MakeItHackin/DEFCON29Badge/pcb.jpg

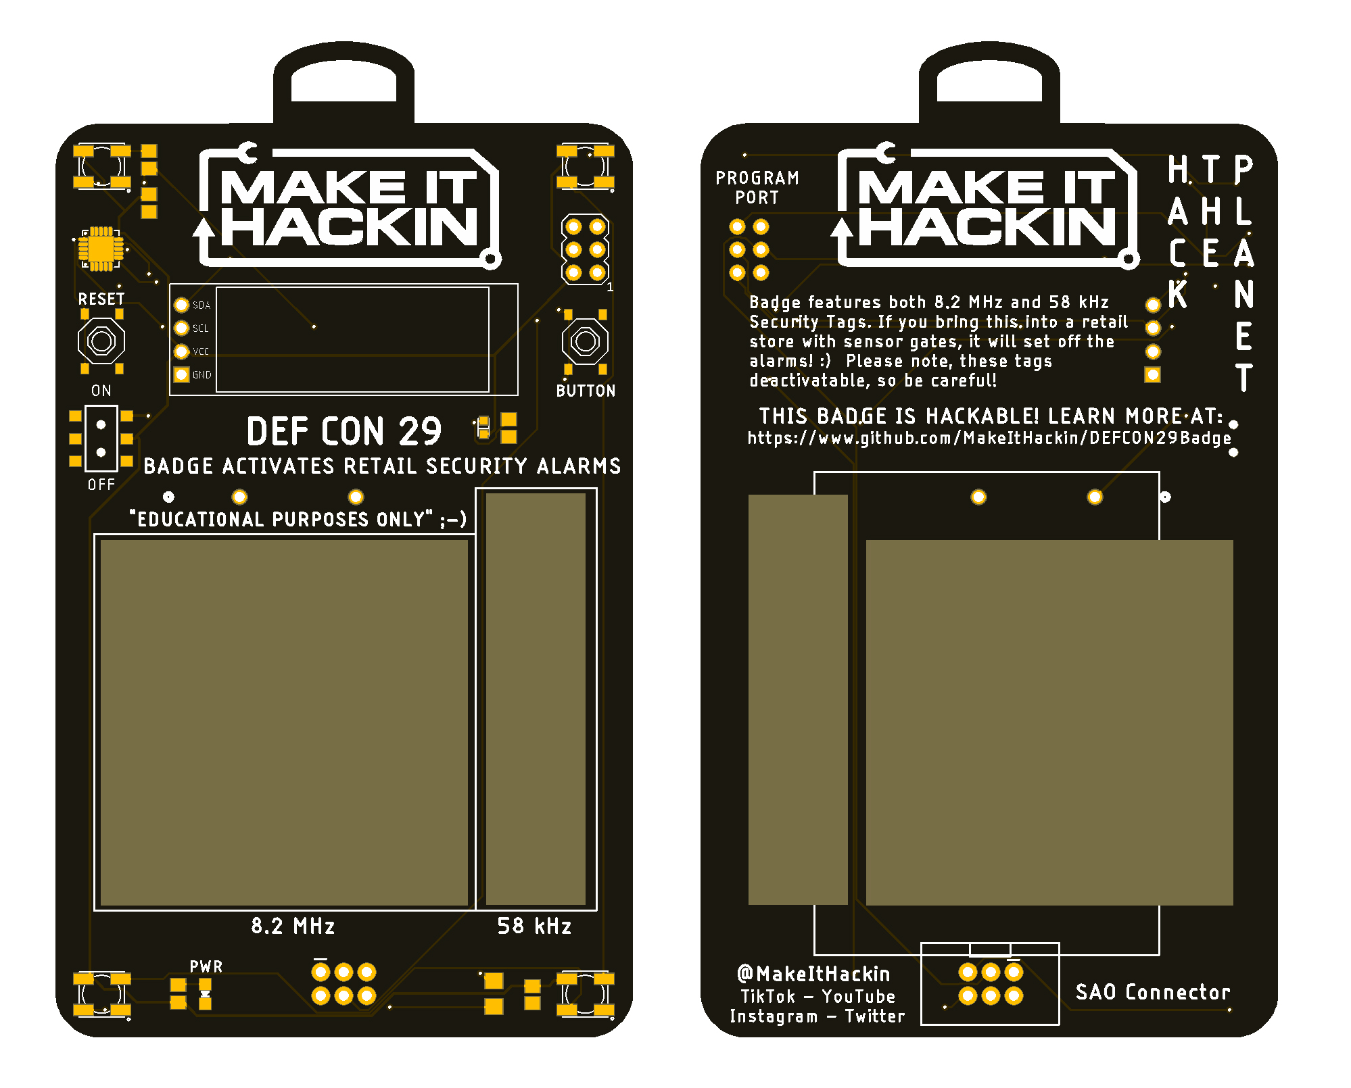
pcb.jpg
