MakeItHackin/DEFCON29Badge/Pictures/Kit/IMG_9323.jpeg

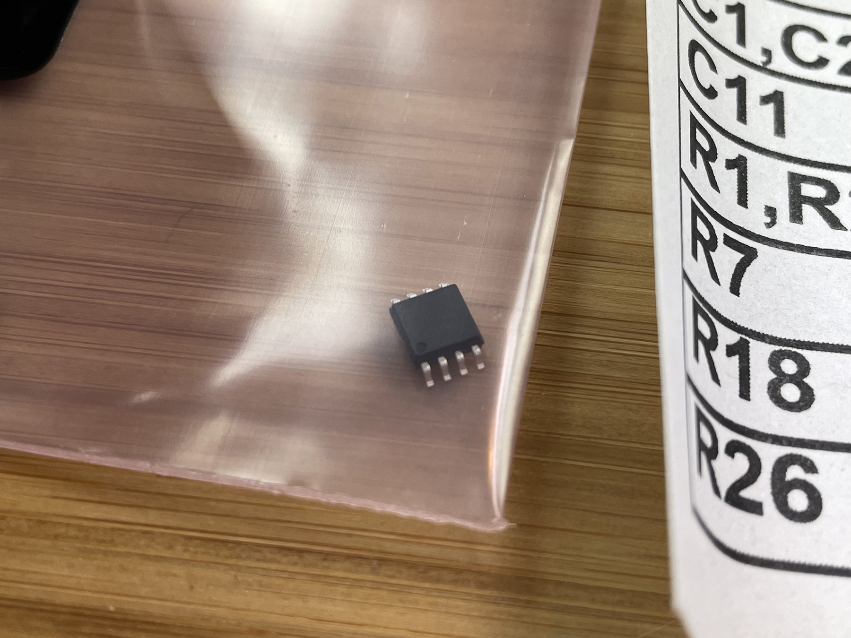
Pictures/Kit/IMG_9323.jpeg
