MakeItHackin/DEFCON29Badge/Pictures/Kit/IMG_9324.jpeg

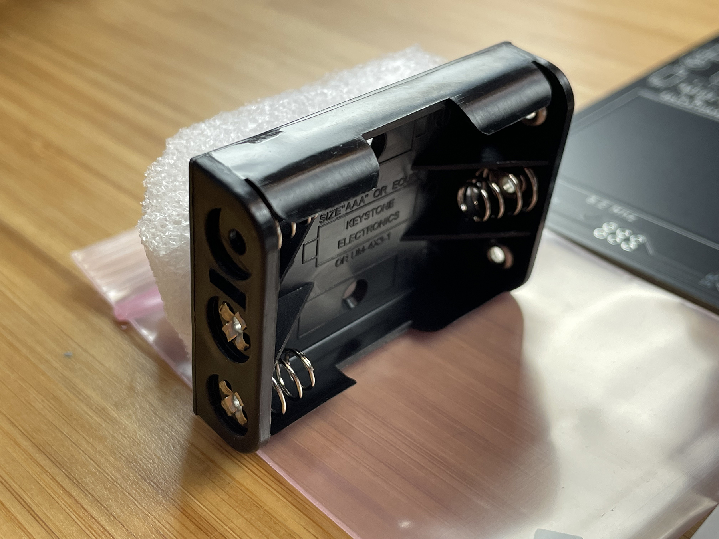
Pictures/Kit/IMG_9324.jpeg
