MakeItHackin/DEFCON29Badge/Pictures/Kit/IMG_9325.jpeg

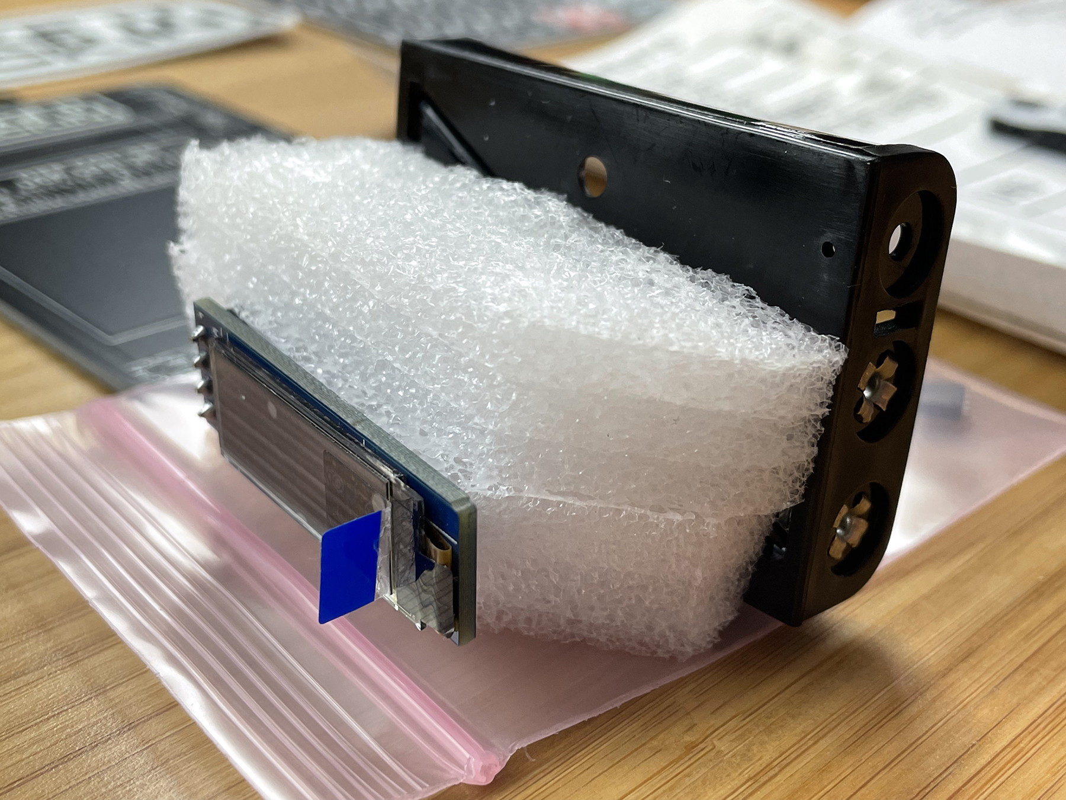
Pictures/Kit/IMG_9325.jpeg
