MakeItHackin/DEFCON29Badge/Pictures/Kit/IMG_9326.jpeg

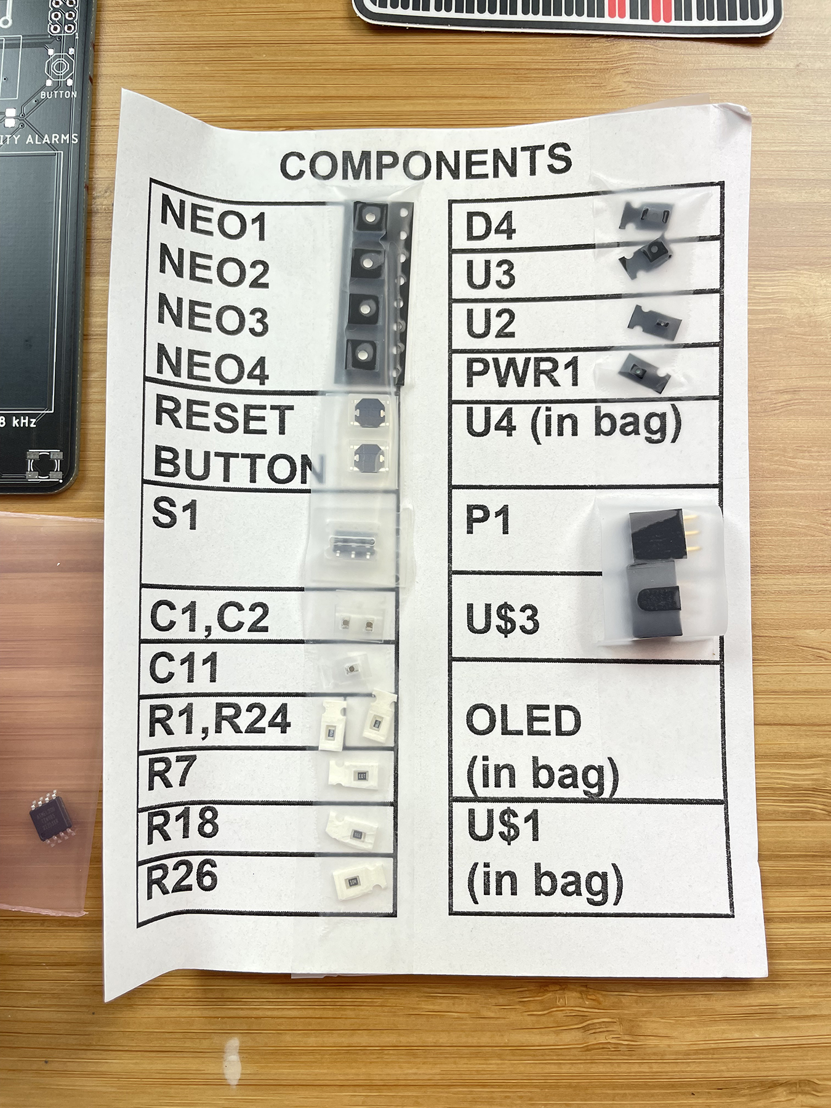
Pictures/Kit/IMG_9326.jpeg
