MakeItHackin/DEFCON29Badge/Pictures/Kit/IMG_9327.jpeg

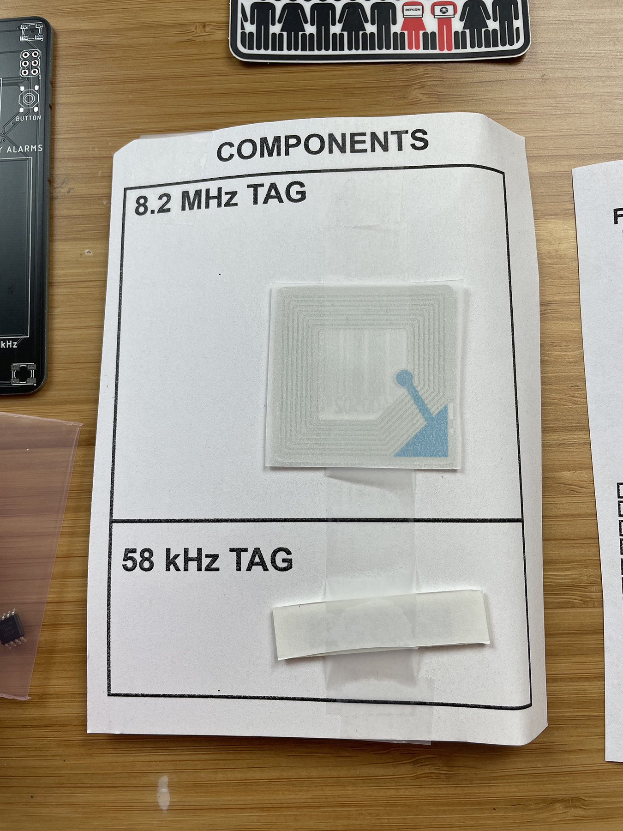
Pictures/Kit/IMG_9327.jpeg
