MakeItHackin/DEFCON29Badge/Pictures/Kit/IMG_9328.jpeg

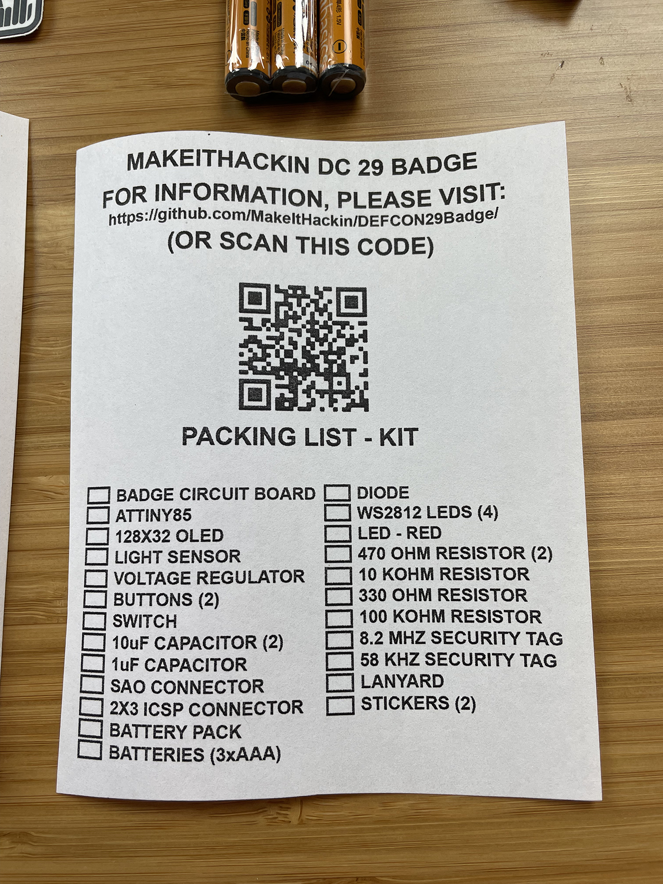
Pictures/Kit/IMG_9328.jpeg
