MakeItHackin/DEFCON29Badge/Pictures/Kit/IMG_9329.jpeg

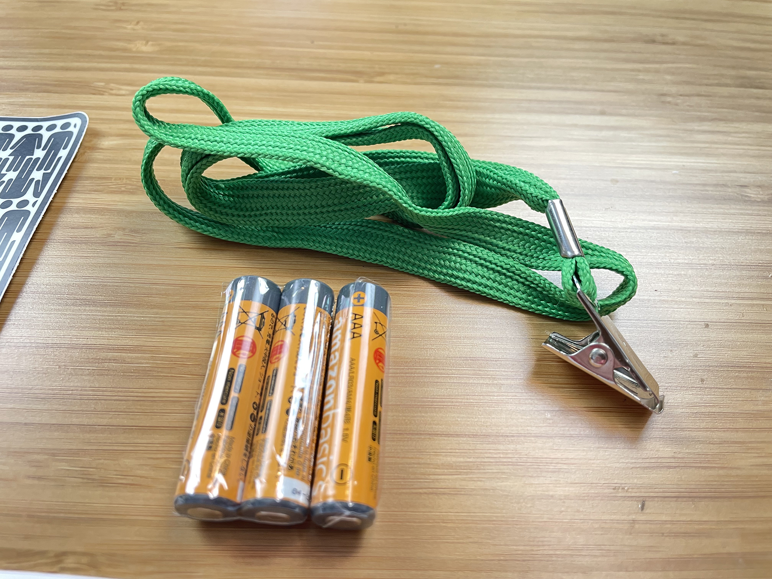
Pictures/Kit/IMG_9329.jpeg
