MakeItHackin/DEFCON29Badge/Pictures/Kit/kit pic.jpg

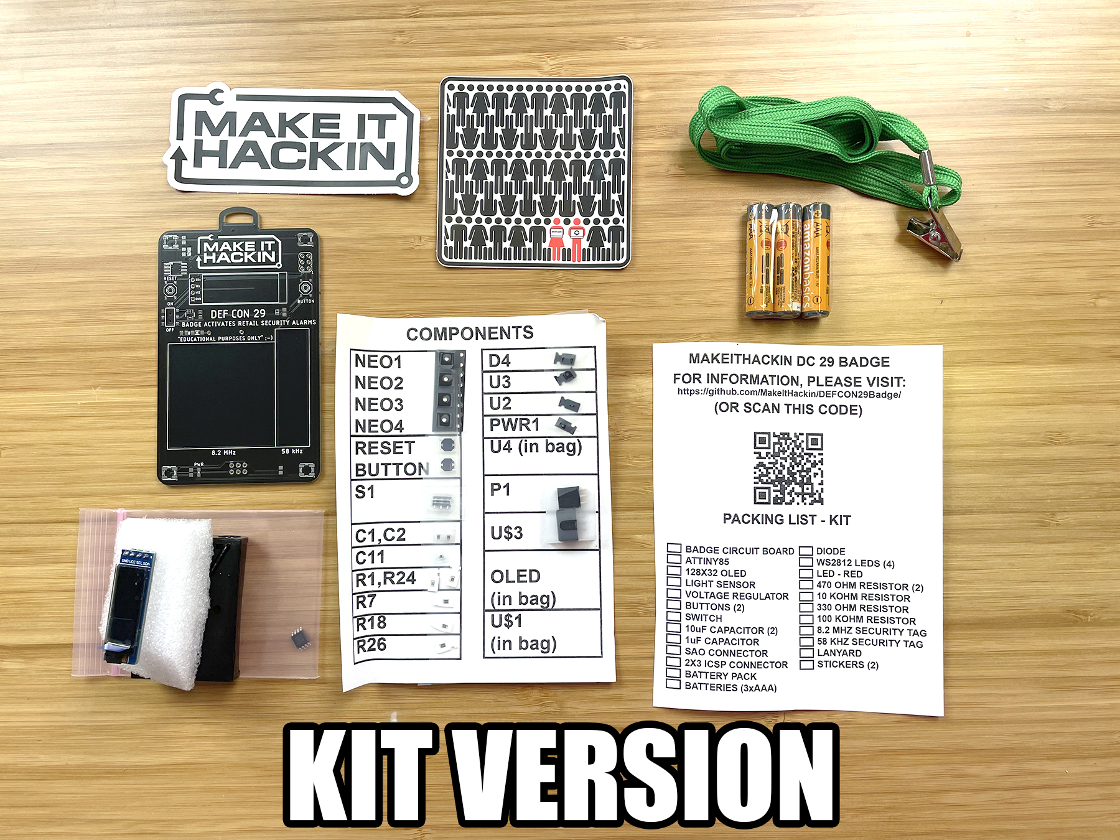
Pictures/Kit/kit pic.jpg
