MakeItHackin/DEFCON29Badge/SAO.jpg

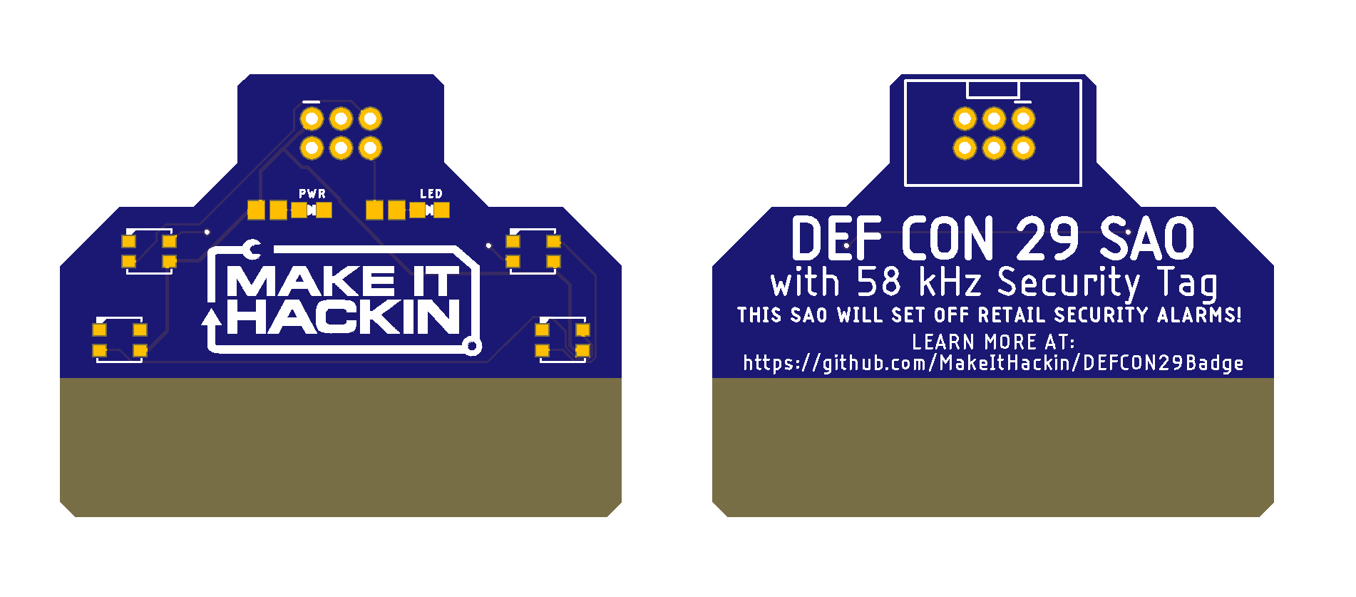
SAO.jpg
