MakeItHackin/DEFCON29Badge/Pictures/FullyAssembled/IMG_9298.jpeg

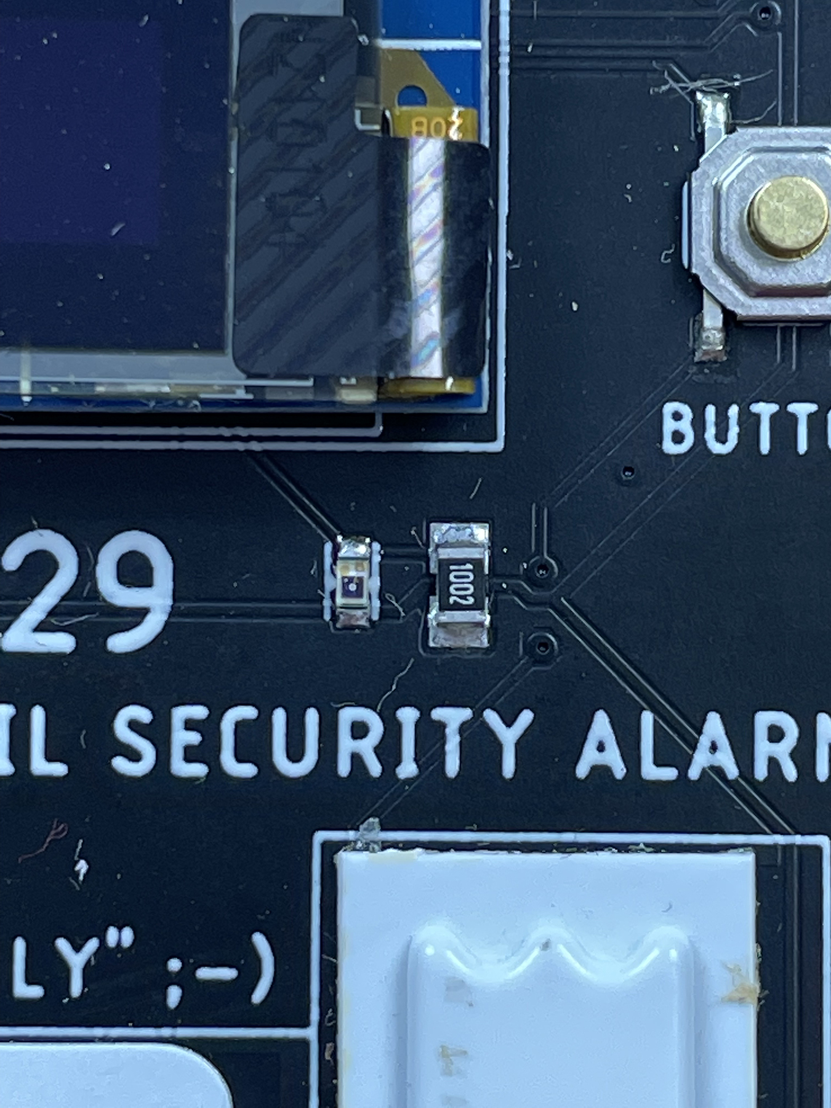
Pictures/FullyAssembled/IMG_9298.jpeg
