MakeItHackin/DEFCON29Badge/Pictures/FullyAssembled/IMG_9299.jpeg

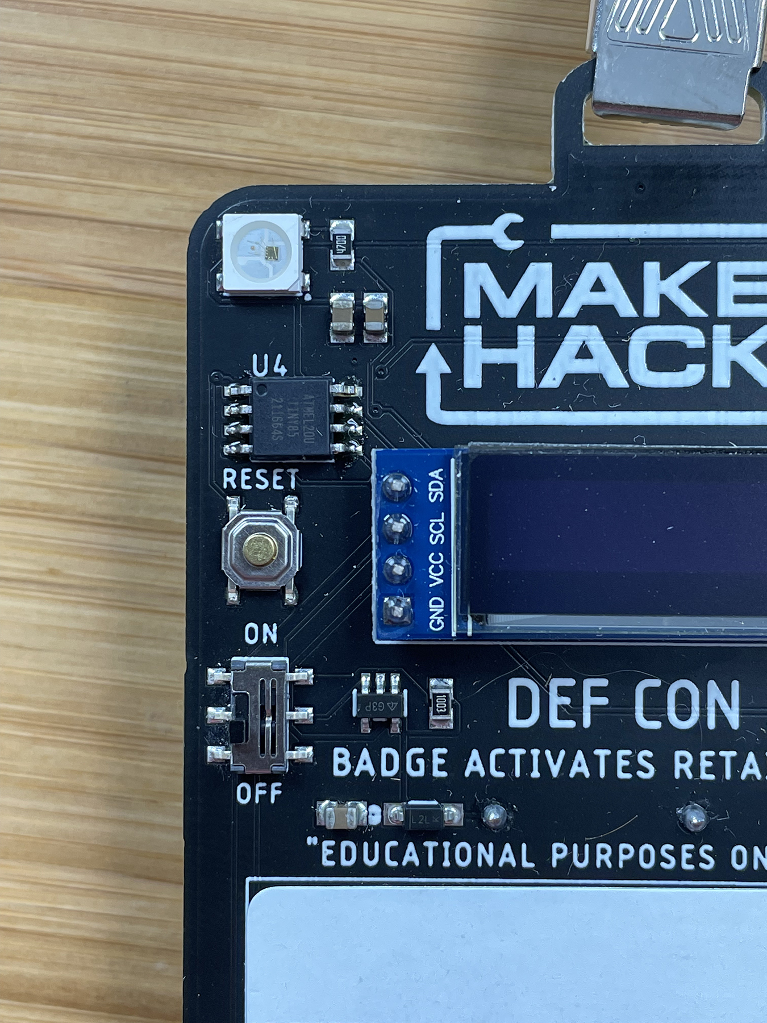
Pictures/FullyAssembled/IMG_9299.jpeg
