MakeItHackin/DEFCON29Badge/Pictures/FullyAssembled/IMG_9300.jpeg

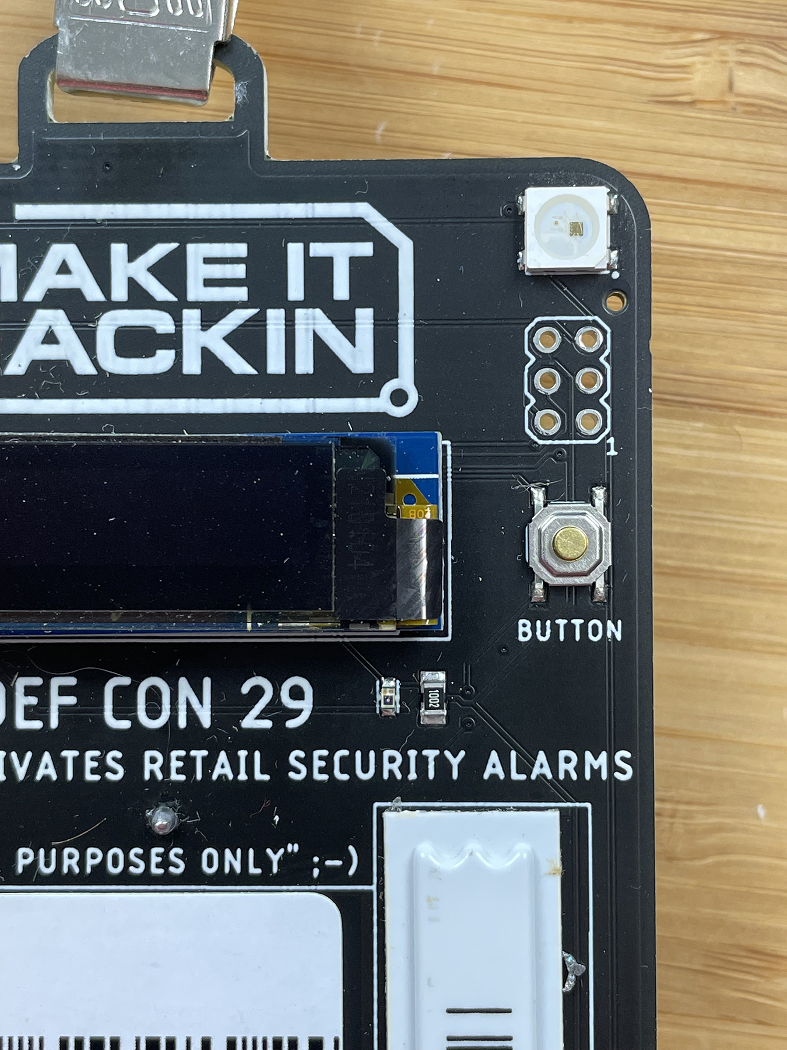
Pictures/FullyAssembled/IMG_9300.jpeg
