MakeItHackin/DEFCON29Badge/Pictures/FullyAssembled/IMG_9301.jpeg

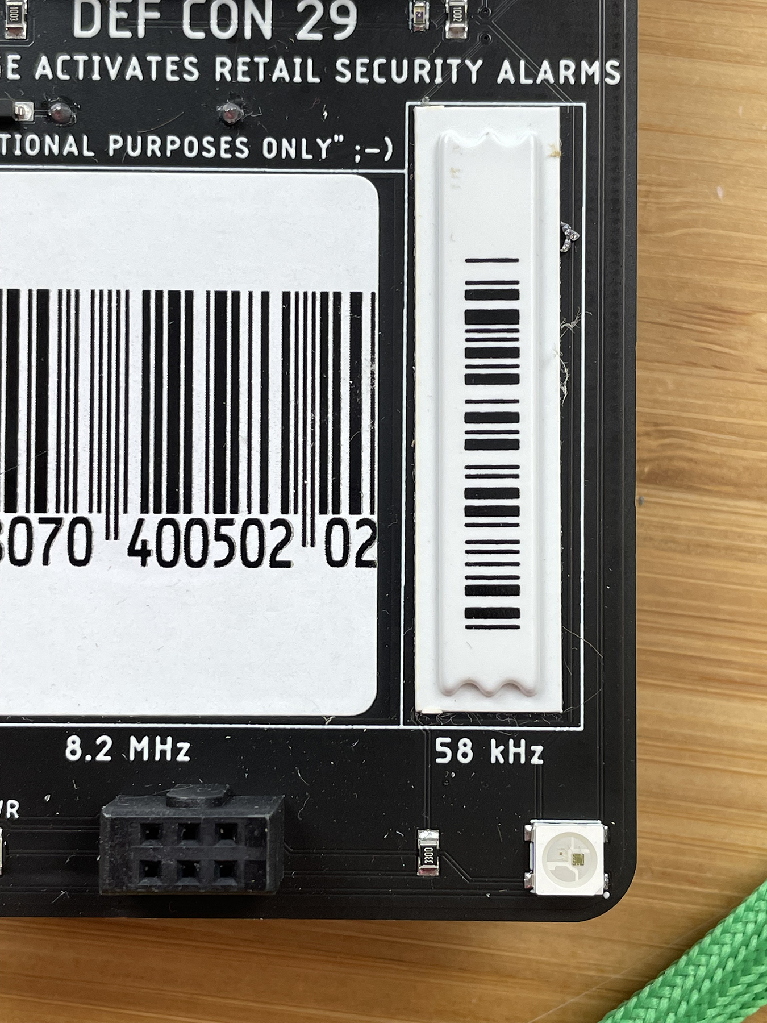
Pictures/FullyAssembled/IMG_9301.jpeg
