MakeItHackin/DEFCON29Badge/Pictures/FullyAssembled/IMG_9302.jpeg

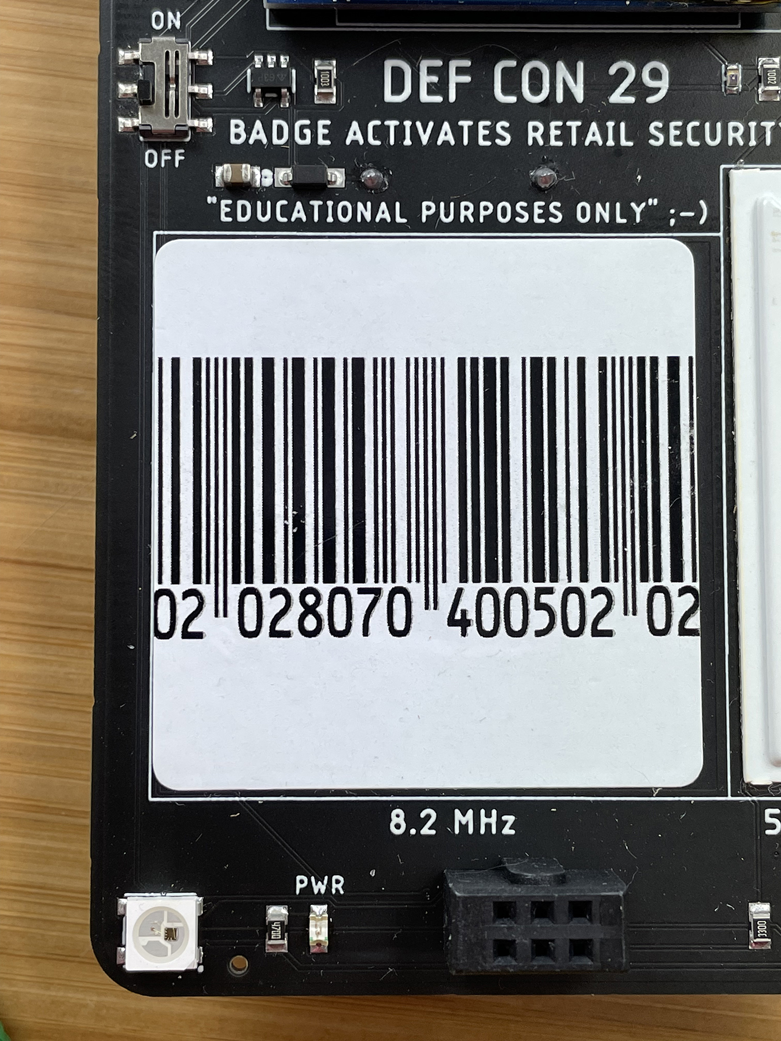
Pictures/FullyAssembled/IMG_9302.jpeg
