MakeItHackin/DEFCON29Badge/Pictures/FullyAssembled/IMG_9311.jpeg

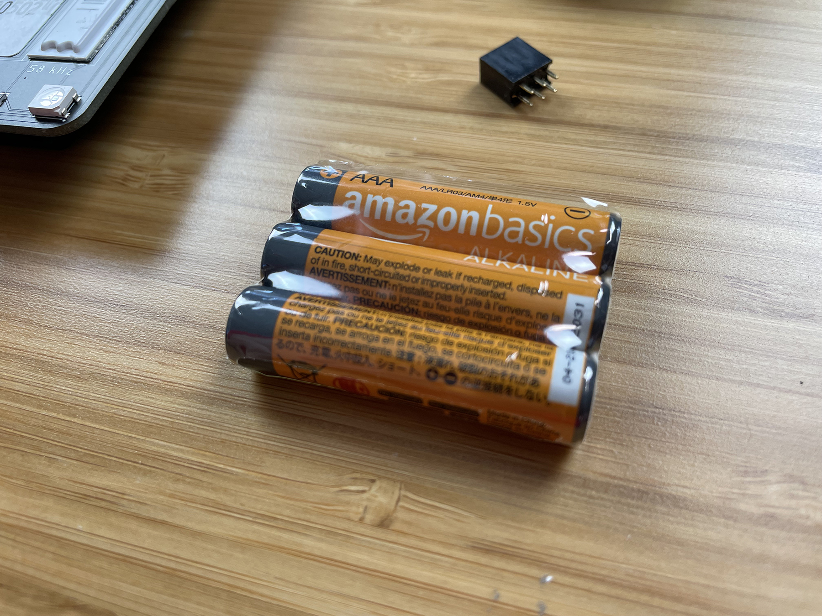
Pictures/FullyAssembled/IMG_9311.jpeg
