MakeItHackin/DEFCON29Badge/Pictures/FullyAssembled/IMG_9312.jpeg

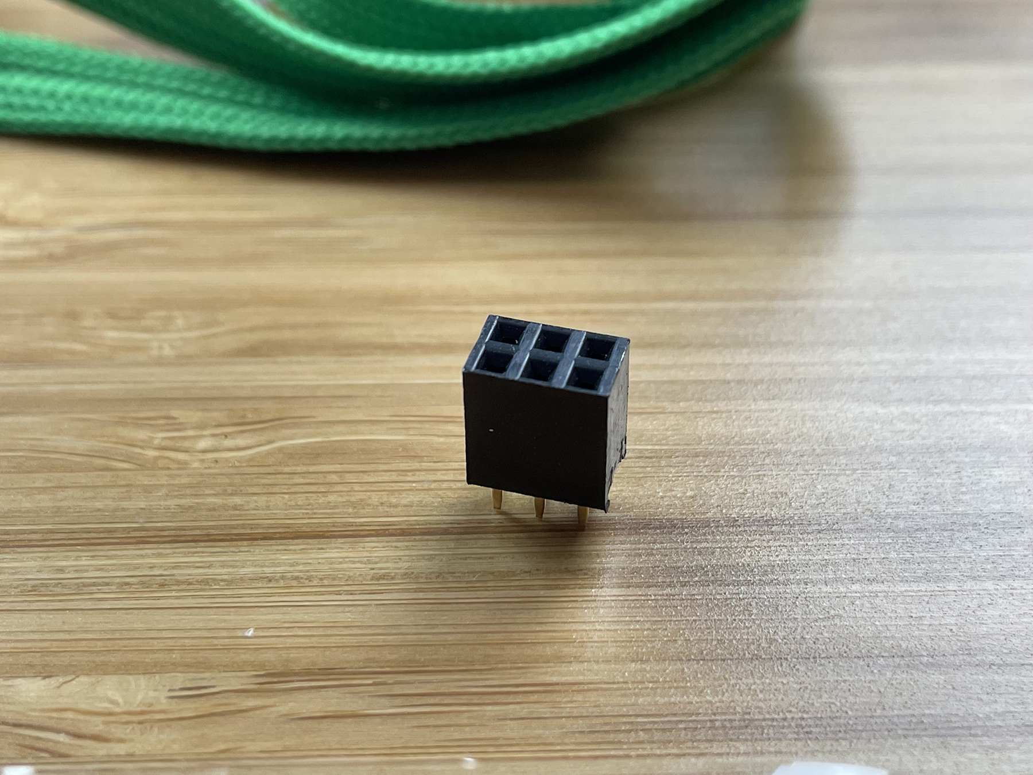
Pictures/FullyAssembled/IMG_9312.jpeg
