MakeItHackin/DEFCON29Badge/Pictures/FullyAssembled/IMG_9315.jpeg

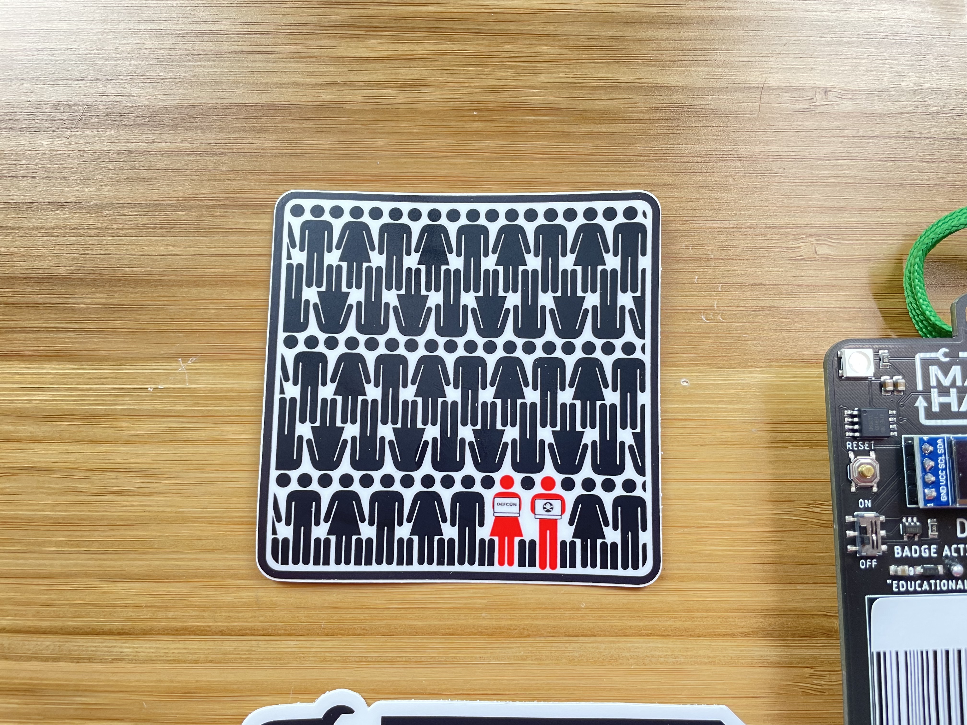
Pictures/FullyAssembled/IMG_9315.jpeg
