MakeItHackin/DEFCON29Badge/Pictures/FullyAssembled/thumb.jpg

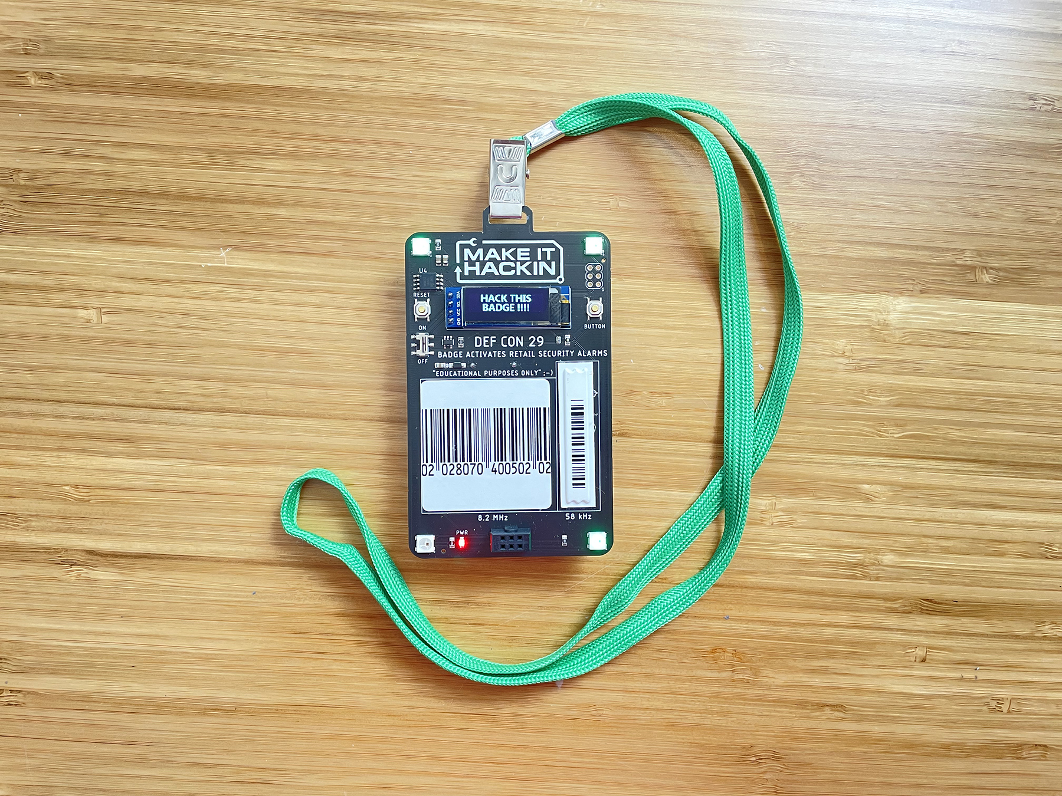
Pictures/FullyAssembled/thumb.jpg
